749/PiKVM-AIMOS-AM-KVM803-UART-Mod/circuit/uart-mod.kicad_sch

## KiCad design circuit/uart-mod.kicad_sch (2024-08-11)

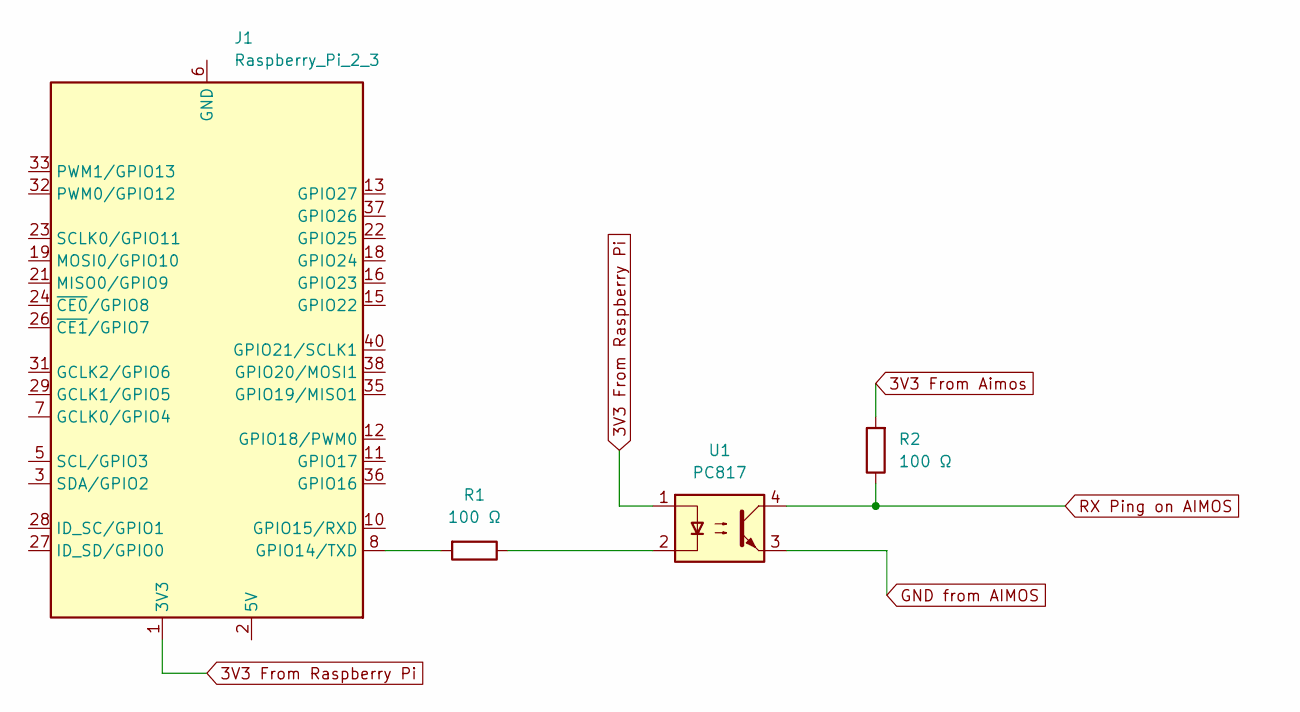
[picture p6: schematic uart-mod.kicad_sch]

Parts:
J1: Raspberry_Pi_2_3
R1, R2: 100 Ω
U1: PC817; DIP-4_W7.62mm

Connections:
3V3 From Aimos: R2.2
3V3 From Raspberry Pi: J1.1 (3V3), J1.17 (3V3), U1.1
GND from AIMOS: U1.3
unnamed: J1.2 (5V), J1.4 (5V)
unnamed: J1.8 (GPIO14/TXD), R1.2
unnamed: J1.6 (GND), J1.9 (GND), J1.14 (GND), J1.20 (GND), J1.25 (GND), J1.30 (GND), J1.34 (GND), J1.39 (GND)
unnamed: R1.1, U1.2
RX Ping on AIMOS: R2.1, U1.4
